RRomaNN/ambient-rgb-led/eeprom_writer_c/eeprom.cpp

#include "eeprom.hpp"

Eeprom::Eeprom()
{

}

uint8_t Eeprom::Ping()
{
  Wire.beginTransmission(EepromAddress);
  Wire.write(0x00);
  return Wire.endTransmission();
}

uint8_t Eeprom::ReadByte(int address)
{
  Wire.beginTransmission(EepromAddress);
  Wire.write((int)(address >> 8));
  Wire.write((int)(address & 0xFF));
  Wire.endTransmission();                  
  Wire.requestFrom((int)EepromAddress, 0x01);
  while (!Wire.available()) 
    delayMicroseconds(IdleTimeUs);
  return Wire.read();
}

uint32_t Eeprom::ReadUint24(int address)
{
  uint32_t result;
  Wire.beginTransmission(EepromAddress);
  Wire.write((int)(address >> 8));
  Wire.write((int)(address & 0xFF));
  Wire.endTransmission();                  
  Wire.requestFrom((int)EepromAddress, 0x03);
  while (!Wire.available()) 
    delayMicroseconds(IdleTimeUs);

  *((uint8_t*)&result) = Wire.read();
  *((uint8_t*)&result + 1) = Wire.read();
  *((uint8_t*)&result + 2) = Wire.read();
  *((uint8_t*)&result + 3) = 0x00;

  return result;
}

void Eeprom::WriteByte(int address, uint8_t data)
{
  Wire.beginTransmission(EepromAddress);
  Wire.write((int)(address >> 8));
  Wire.write((int)(address & 0xFF));
  Wire.write(data);
  Wire.endTransmission();  

  uint8_t busStatus = 0xFF;
  do       
  {
    Wire.beginTransmission(EepromAddress);
    busStatus = Wire.endTransmission();
  }
  while (busStatus != 0x00);
}

void Eeprom::WriteUint24(int address, uint32_t data)
{
  Wire.beginTransmission(EepromAddress);
  Wire.write((int)(address >> 8));
  Wire.write((int)(address & 0xFF));
  Wire.write(*((uint8_t*)&data));
  Wire.write(*((uint8_t*)&data + 1));
  Wire.write(*((uint8_t*)&data + 2));
  Wire.endTransmission();  

  uint8_t busStatus = 0xFF;
  do       
  {
    Wire.beginTransmission(EepromAddress);
    busStatus = Wire.endTransmission();
  }
  while (busStatus != 0x00);
}

void Eeprom::ReadDataBlock(int address, uint8_t* data)
{
  Wire.beginTransmission(EepromAddress);
  Wire.write((int)(address >> 8));   // MSB
  Wire.write((int)(address & 0xFF)); // LSB
  Wire.endTransmission();   
  {
    Wire.requestFrom((int)EepromAddress, (int)RwBlockSize);
    while (!Wire.available()) 
      delayMicroseconds(IdleTimeUs);

    for(int i = 0; i < RwBlockSize; ++i)
      data[i] = Wire.read();
  }
}

void Eeprom::ReadImageBlock(uint8_t pattern_index, uint8_t row, uint8_t block_number, uint8_t* data)
{
  int address = (pattern_index == 0) 
    ? Pattern2ColorAddress + row * 0x20 + block_number * RwBlockSize
    : Pattern4ColorAddress + row * 0x40 + block_number * RwBlockSize;

  ReadDataBlock(address, data);
}

void Eeprom::ReadSavedSettings(uint8_t* selected_pattern, uint8_t* selected_color2, uint8_t* selected_color4, uint8_t* selected_speed, uint8_t* selected_led_count, bool* preview_colors, bool* is_rgbw_strip)
{
  *selected_pattern = ReadByte(SelectedPatternAddress);
  *selected_color2 = ReadByte(Selected2ColorAddress);
  *selected_color4 = ReadByte(Selected4ColorAddress);
  *selected_speed = ReadByte(SelectedSpeedAddress);
  *selected_led_count = ReadByte(LedCountAddress);
  *preview_colors = ReadByte(PreviewLedAddress) > 0;
  *is_rgbw_strip = ReadByte(IsRgbwTypeLedAddress) > 0;
}

void Eeprom::SaveSettings(uint8_t selected_pattern, uint8_t selected_color2, uint8_t selected_color4, uint8_t selected_speed, uint8_t selected_led_count, bool preview_colors, bool is_rgbw_strip)
{
  WriteByte(SelectedPatternAddress, selected_pattern);
  WriteByte(Selected2ColorAddress, selected_color2);
  WriteByte(Selected4ColorAddress, selected_color4);
  WriteByte(SelectedSpeedAddress, selected_speed);
  WriteByte(LedCountAddress, selected_led_count);
  WriteByte(PreviewLedAddress, preview_colors ? 0x01 : 0x00);
  WriteByte(IsRgbwTypeLedAddress, is_rgbw_strip ? 0x01 : 0x00);
}

void Eeprom::ReadColor2Schema(uint8_t color_num, uint32_t* color_a, uint32_t* color_b)
{
  int address = Schemas2ColorAddress + color_num * 0x6;
  *color_a = ReadUint24(address);
  *color_b = ReadUint24(address + 0x3);
}

void Eeprom::ReadColor4Schema(uint8_t color_num, uint32_t* color_a, uint32_t* color_b, uint32_t* color_c, uint32_t* color_d)
{
  int address = Schemas4ColorAddress + color_num * 0xC;
  *color_a = ReadUint24(address);
  *color_b = ReadUint24(address + 0x3);
  *color_c = ReadUint24(address + 0x6);
  *color_d = ReadUint24(address + 0x9);
}

void Eeprom::SaveColor2Schema(uint8_t color_num, uint32_t color_a, uint32_t color_b)
{
  int address = Schemas2ColorAddress + color_num * 0x6;
  WriteUint24(address, color_a);
  WriteUint24(address + 0x3, color_b);
}
    
void Eeprom::SaveColor4Schema(uint8_t color_num, uint32_t color_a, uint32_t color_b, uint32_t color_c, uint32_t color_d)
{
  int address = Schemas4ColorAddress + color_num * 0xC;
  WriteUint24(address, color_a);
  WriteUint24(address + 0x3, color_b);
  WriteUint24(address + 0x6, color_c);
  WriteUint24(address + 0x9, color_d);
}
