RRomaNN/ambient-rgb-led/eeprom_writer_c/eeprom.hpp

#ifndef __EEPROM__
#define __EEPROM__

#include "global.hpp"

static const uint8_t EepromAddress = 0x50;
static const uint8_t RwBlockSize  =  0x10;
static const uint8_t Pattern2ColorsRowSize  =  0x20;
static const uint8_t Pattern4ColorsRowSize  =  0x40;

static const uint16_t Pattern2ColorAddress   = 0x0000;
static const uint16_t Pattern4ColorAddress   = 0x2000;
static const uint16_t Schemas2ColorAddress   = 0x6000;
static const uint16_t Schemas4ColorAddress   = 0x60C0;
static const uint16_t SelectedPatternAddress = 0x6240;
static const uint16_t Selected2ColorAddress  = 0x6241;
static const uint16_t Selected4ColorAddress  = 0x6242;
static const uint16_t SelectedSpeedAddress   = 0x6243;
static const uint16_t LedCountAddress        = 0x6244; 
static const uint16_t PreviewLedAddress      = 0x6245; 
static const uint16_t IsRgbwTypeLedAddress   = 0x6246; 

class Eeprom
{
  public:
    Eeprom();

    uint8_t Ping();
    void ReadSavedSettings(uint8_t* selected_pattern, uint8_t* selected_color2, uint8_t* selected_color4, uint8_t* selected_speed, uint8_t* selected_led_count, bool* preview_colors, bool* is_rgbw_strip);
    void SaveSettings(uint8_t selected_pattern, uint8_t selected_color2, uint8_t selected_color4, uint8_t selected_speed, uint8_t selected_led_count, bool preview_colors, bool is_rgbw_strip);
    void ReadColor2Schema(uint8_t color_num, uint32_t* color_a, uint32_t* color_b);
    void ReadColor4Schema(uint8_t color_num, uint32_t* color_a, uint32_t* color_b, uint32_t* color_c, uint32_t* color_d);
    void SaveColor2Schema(uint8_t color_num, uint32_t color_a, uint32_t color_b);
    void SaveColor4Schema(uint8_t color_num, uint32_t color_a, uint32_t color_b, uint32_t color_c, uint32_t color_d);
    void ReadImageBlock(uint8_t pattern_index, uint8_t row, uint8_t block_number, uint8_t* data);

  private:
    uint8_t ReadByte(int address);
    uint32_t ReadUint24(int address);
    void WriteByte(int address, uint8_t data);
    void WriteUint24(int address, uint32_t data);
    void ReadDataBlock(int address, uint8_t* data);
};

#define LPEeprom Eeprom*

#endif
